DmitrySazonov/ka-radio-player/images/image02.jpeg

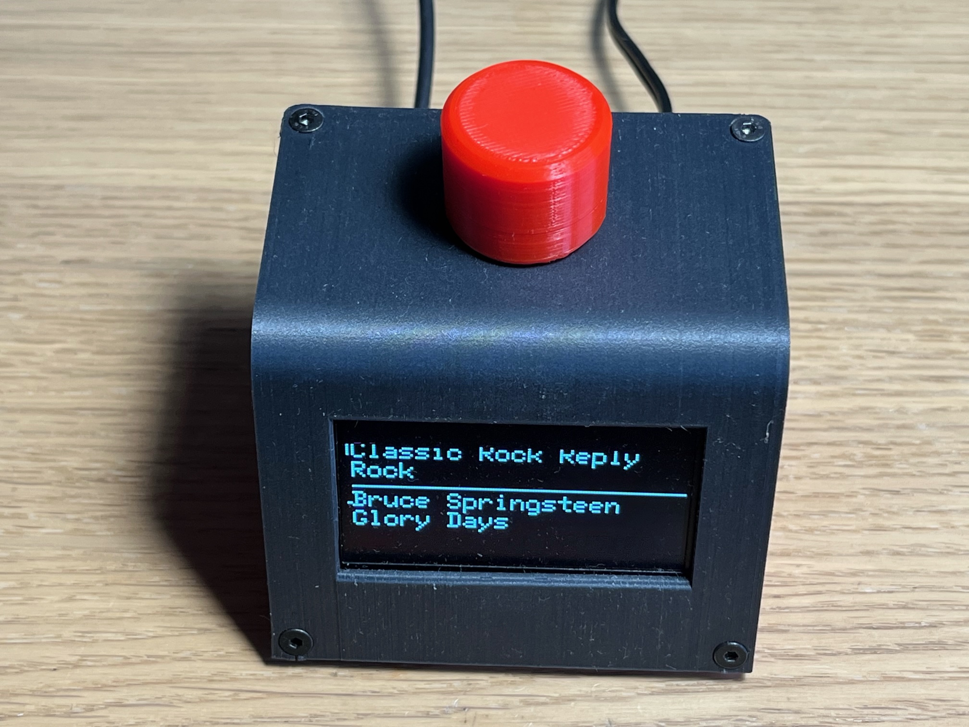
images/image02.jpeg
