DmitrySazonov/ka-radio-player/images/image03.jpeg

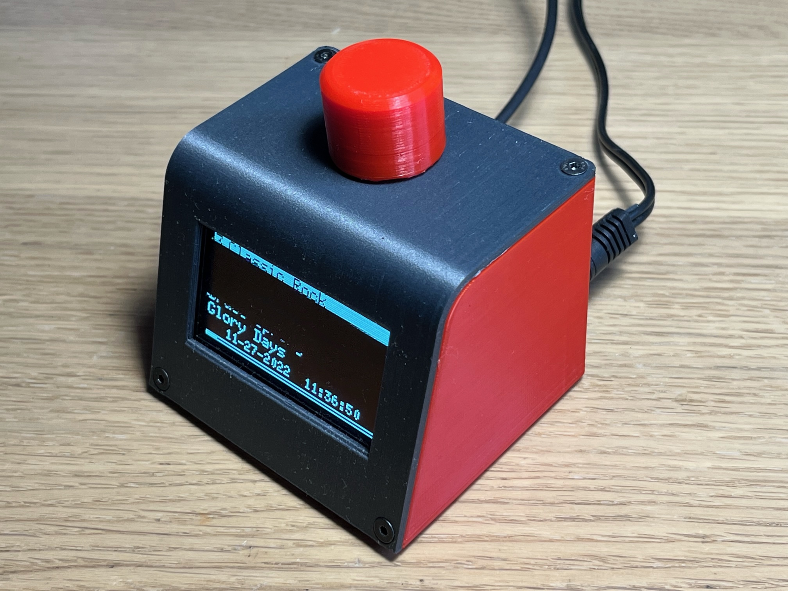
images/image03.jpeg
