DmitrySazonov/ka-radio-player/images/image04.jpeg

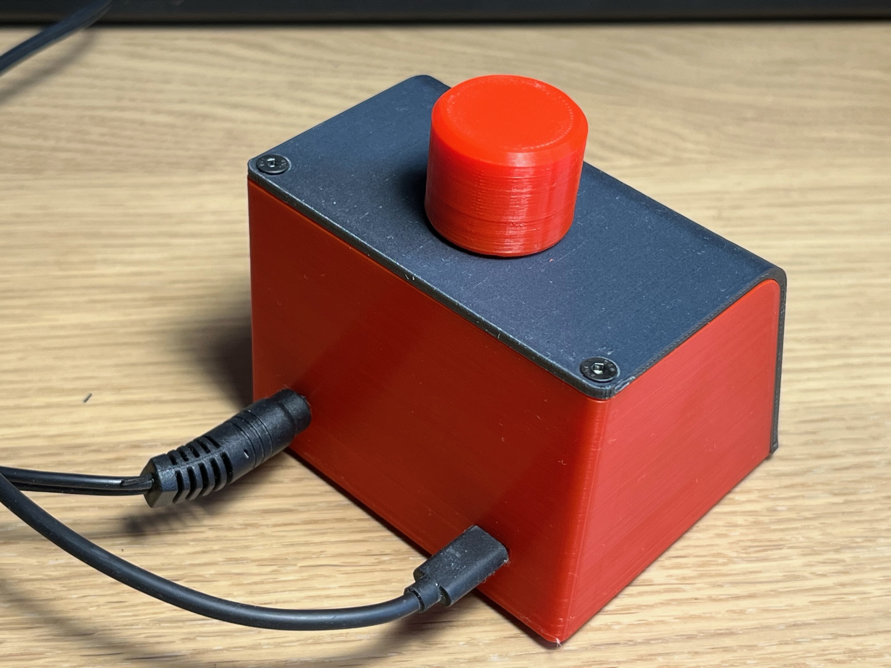
images/image04.jpeg
