DmitrySazonov/ka-radio-player/images/image05.jpeg

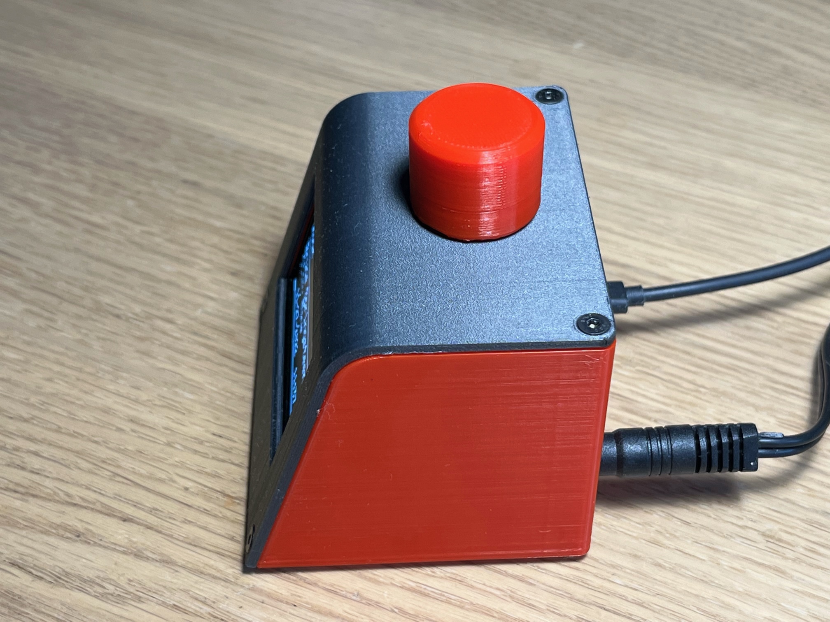
images/image05.jpeg
