DmitrySazonov/ka-radio-player/images/image06.jpeg

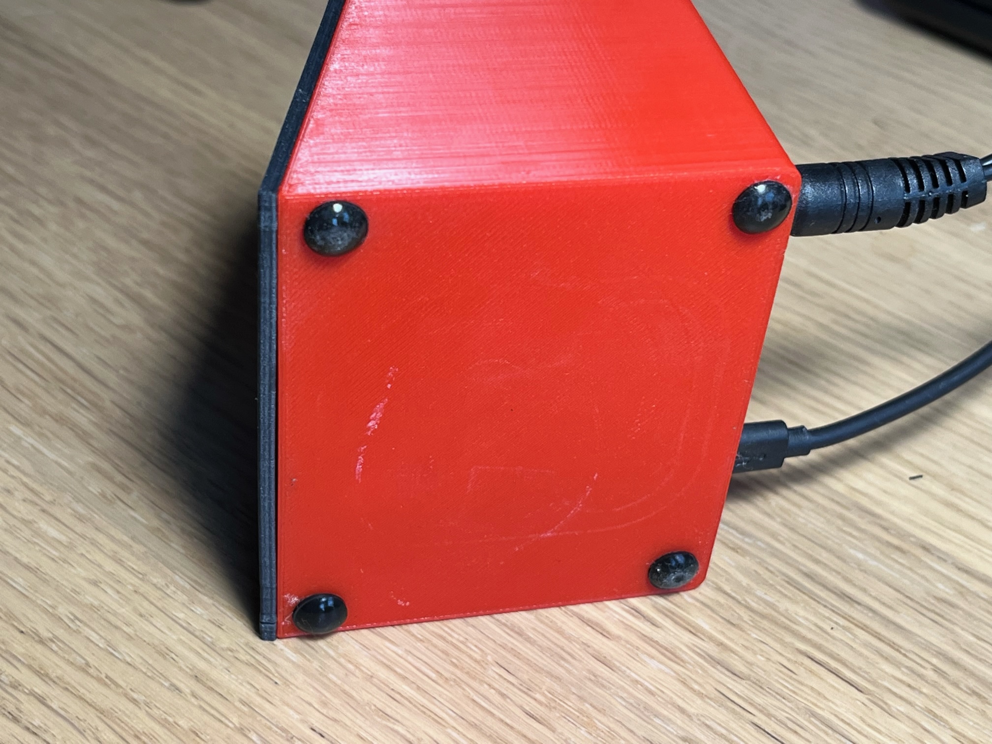
images/image06.jpeg
