DmitrySazonov/ka-radio-player/images/image07.jpeg

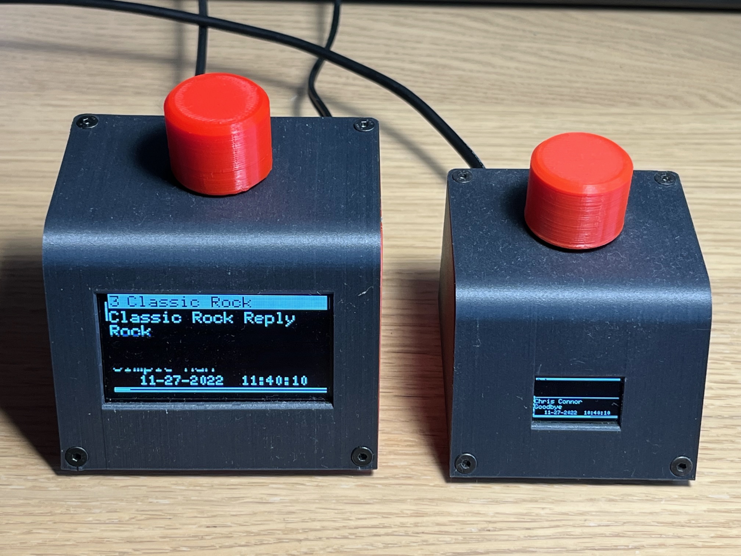
images/image07.jpeg
