DmitrySazonov/ka-radio-player/images/image08.jpeg

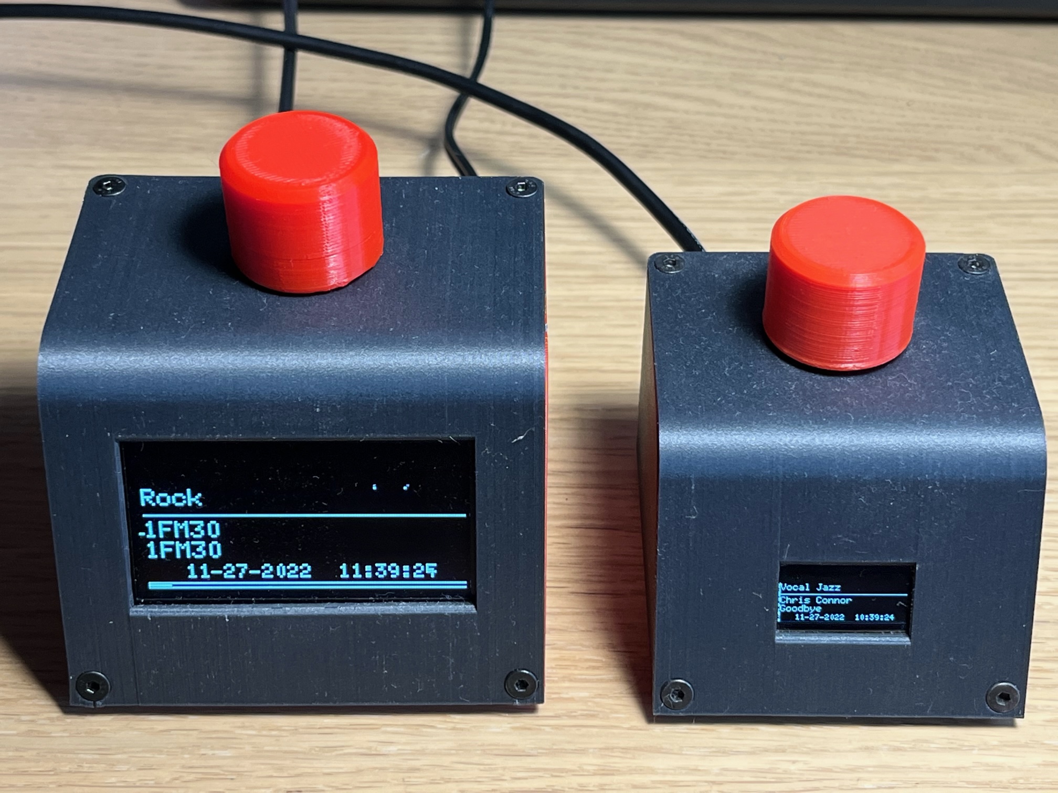
images/image08.jpeg
