DmitrySazonov/ka-radio-player/images/image10.jpeg

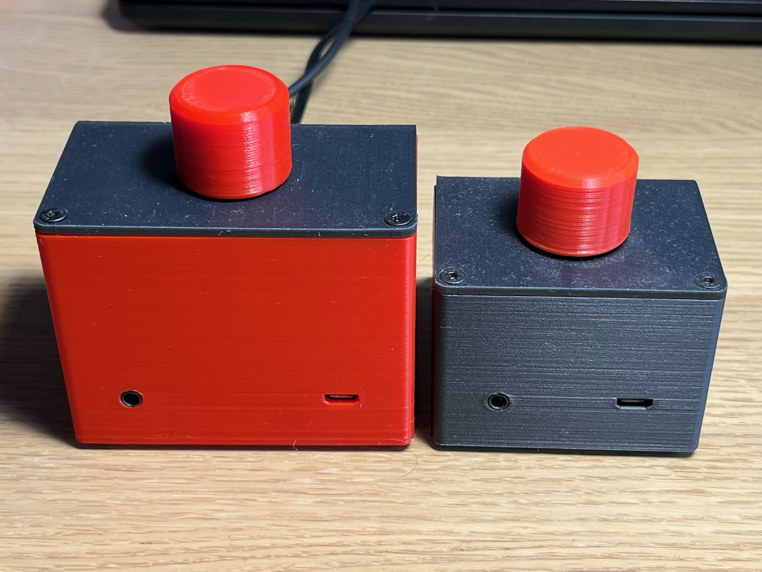
images/image10.jpeg
