DmitrySazonov/ka-radio-player/images/v2/image1.jpeg

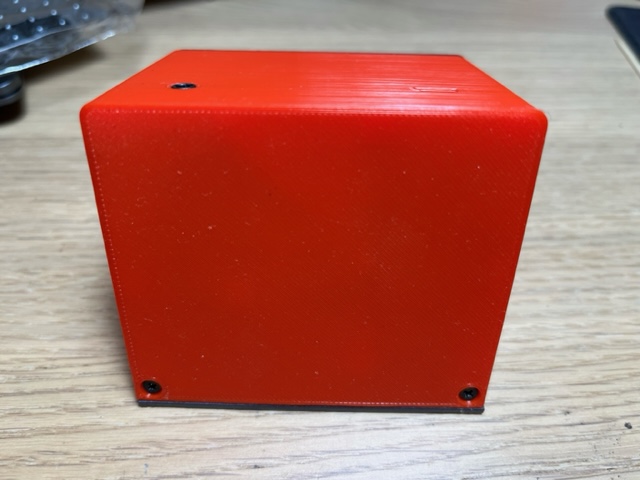
images/v2/image1.jpeg
