DmitrySazonov/ka-radio-player/images/v2/image2.jpeg

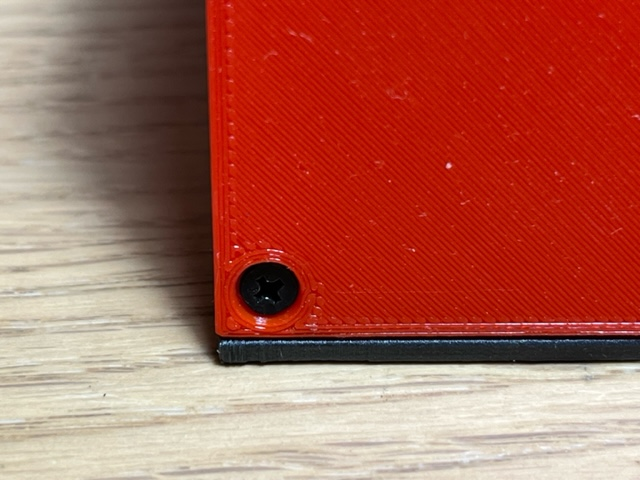
images/v2/image2.jpeg
